jasonsbeer/Amiga-2000-EATX/DataSheets/ISA_Bus_pins.png

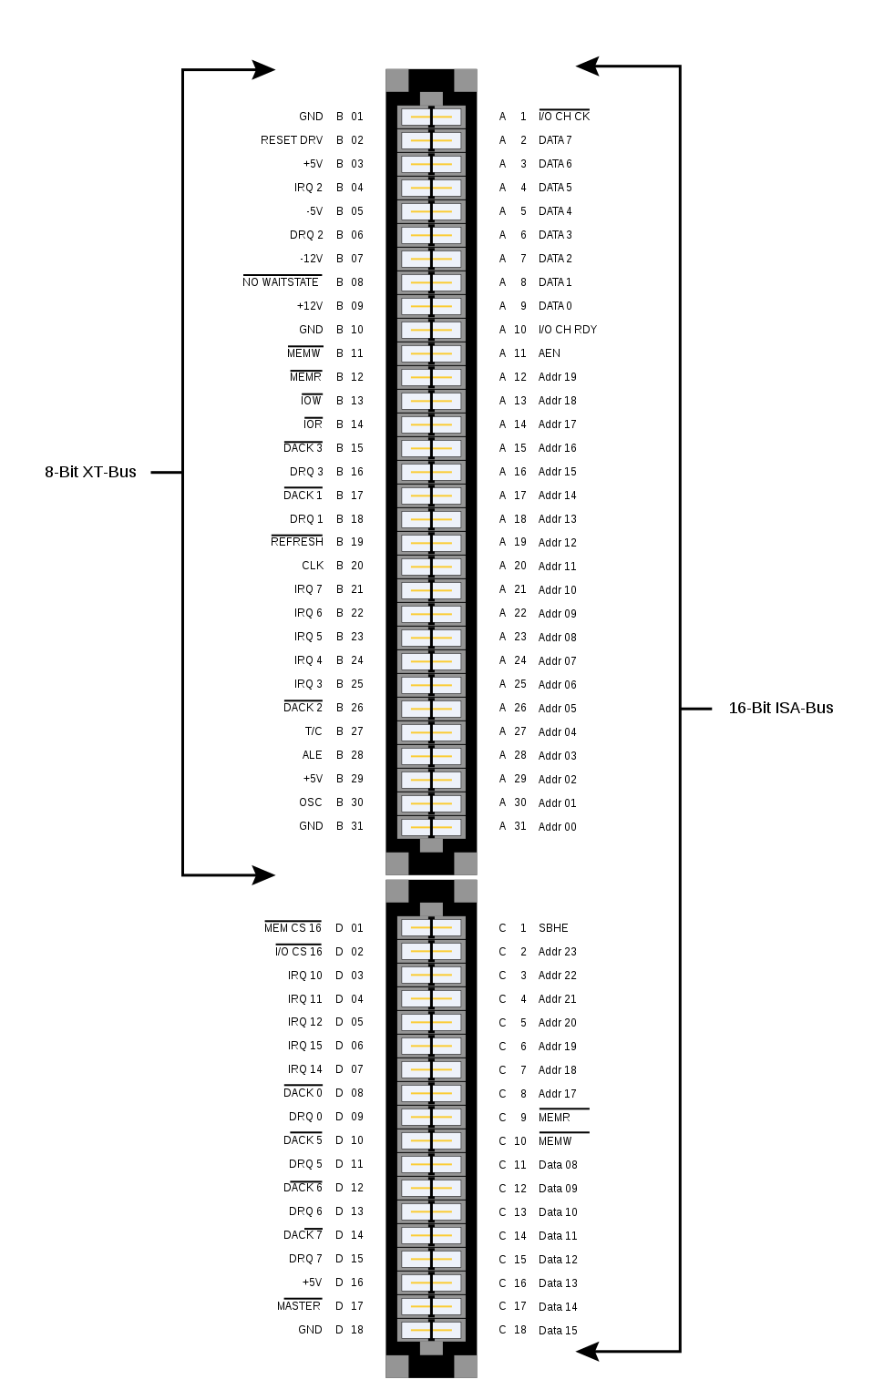
DataSheets/ISA_Bus_pins.png
