jasonsbeer/Amiga-2000-EATX/Images/2000ATX.png

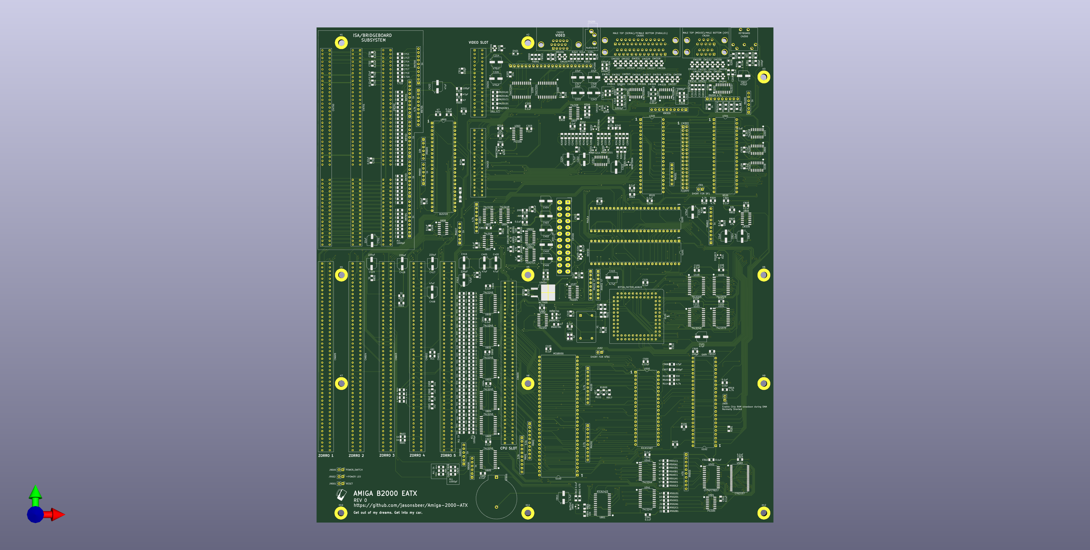
Images/2000ATX.png
