jasonsbeer/Amiga-2000-EATX/Images/2000EATX-Rev121.png

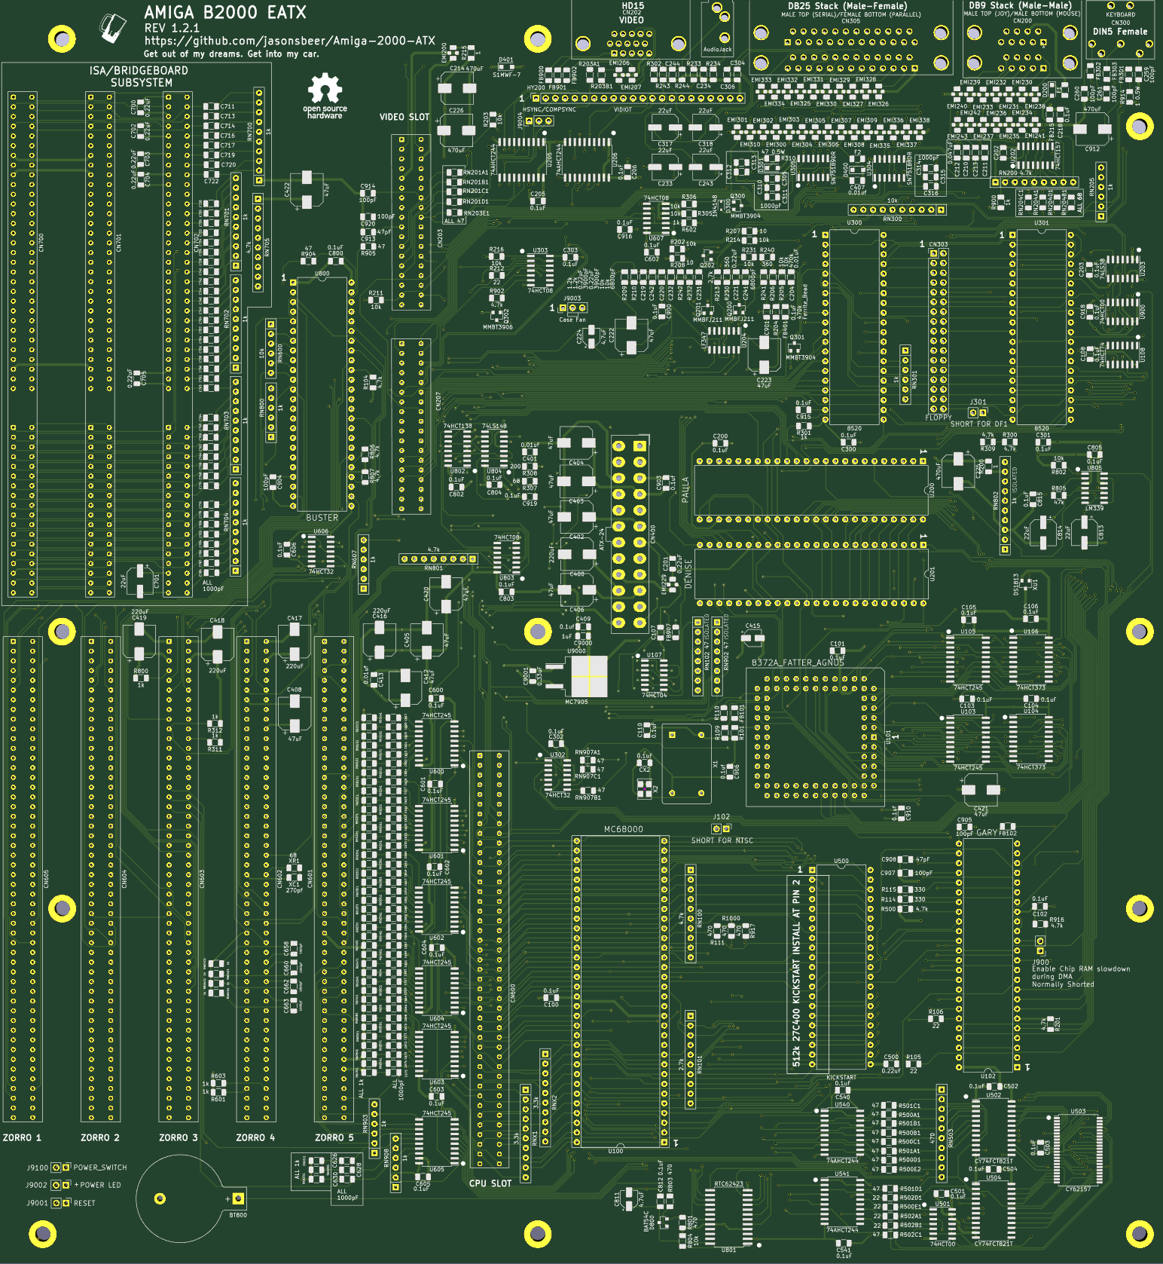
Images/2000EATX-Rev121.png
