jasonsbeer/Amiga-2000-EATX/Images/A2000EATX.png

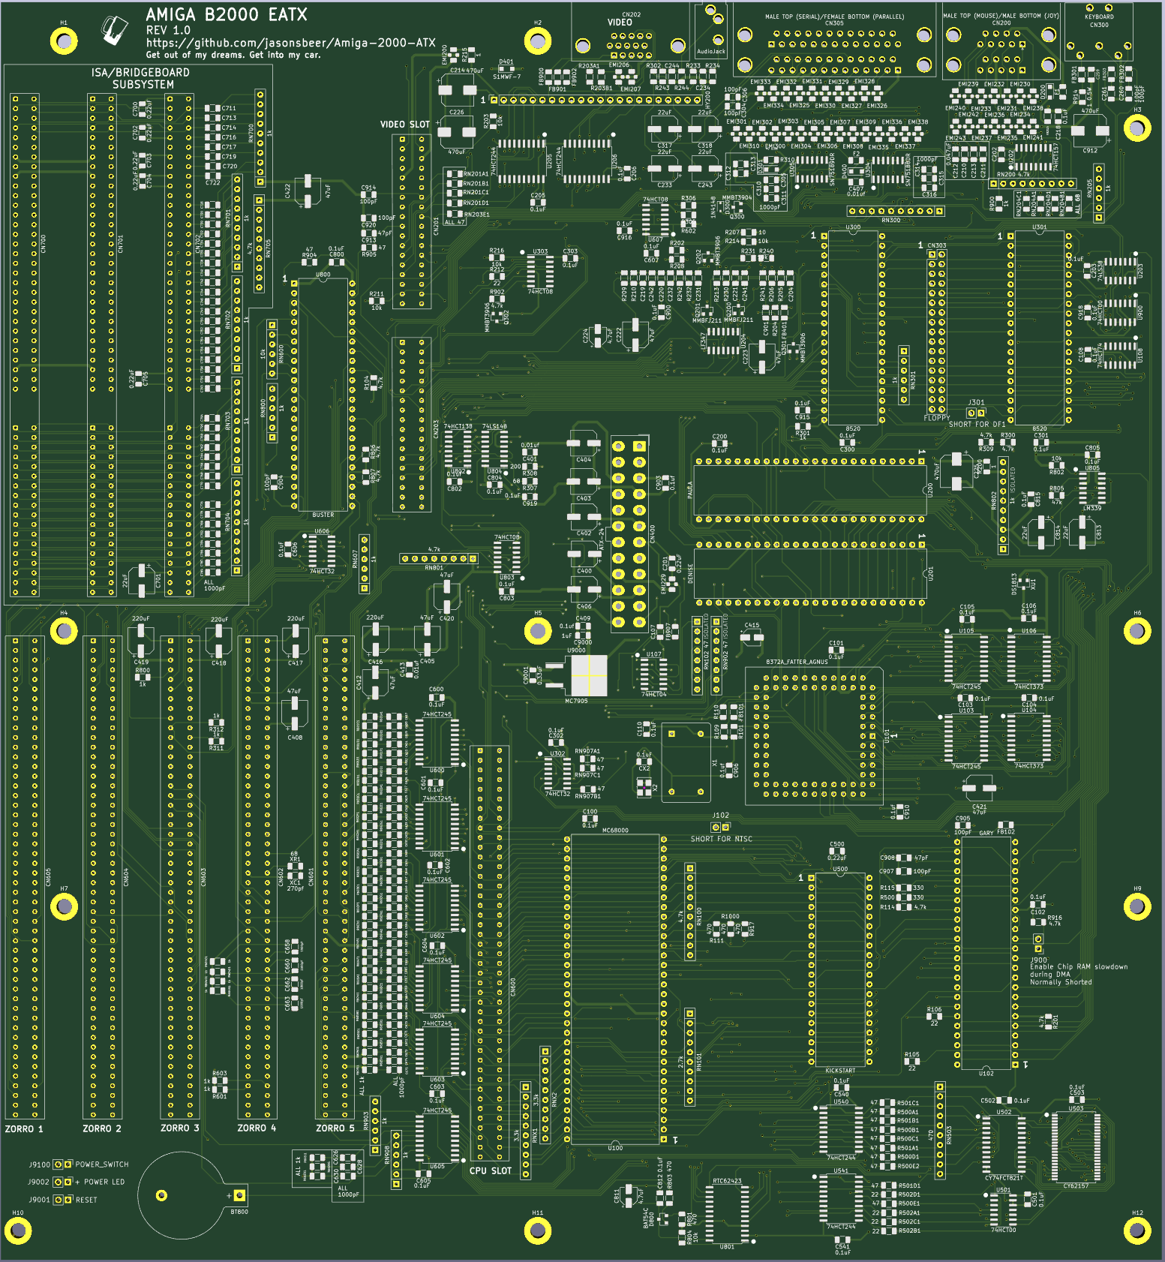
Images/A2000EATX.png
