jasonsbeer/Amiga-2000-EATX/Images/aibb.jpg

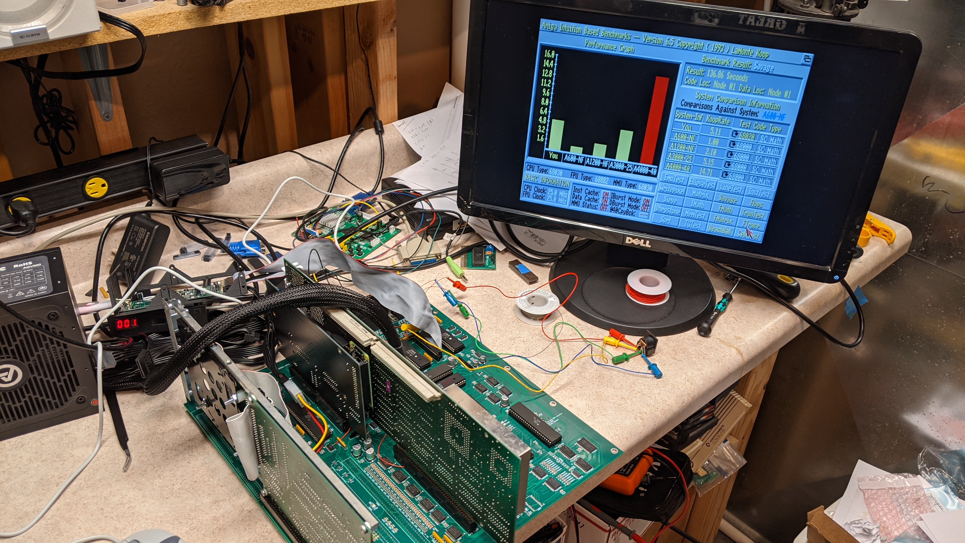
Images/aibb.jpg
