jasonsbeer/Amiga-2000-EATX/Images/Green.jpg

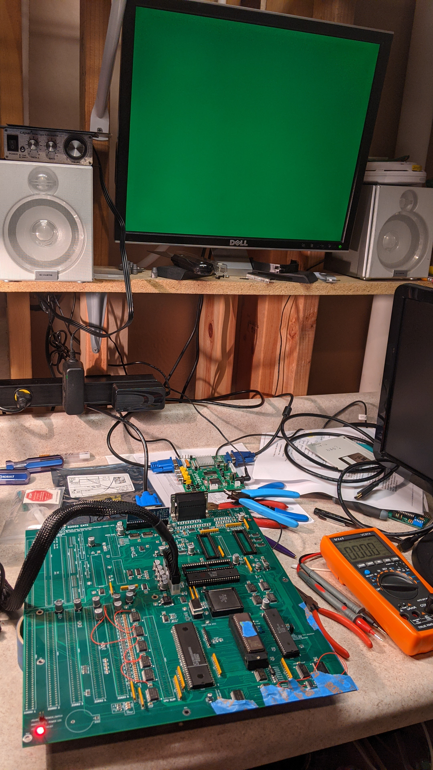
Images/Green.jpg
